Supermagnum/Tandberg/TDV-5000/tandberg.jpg

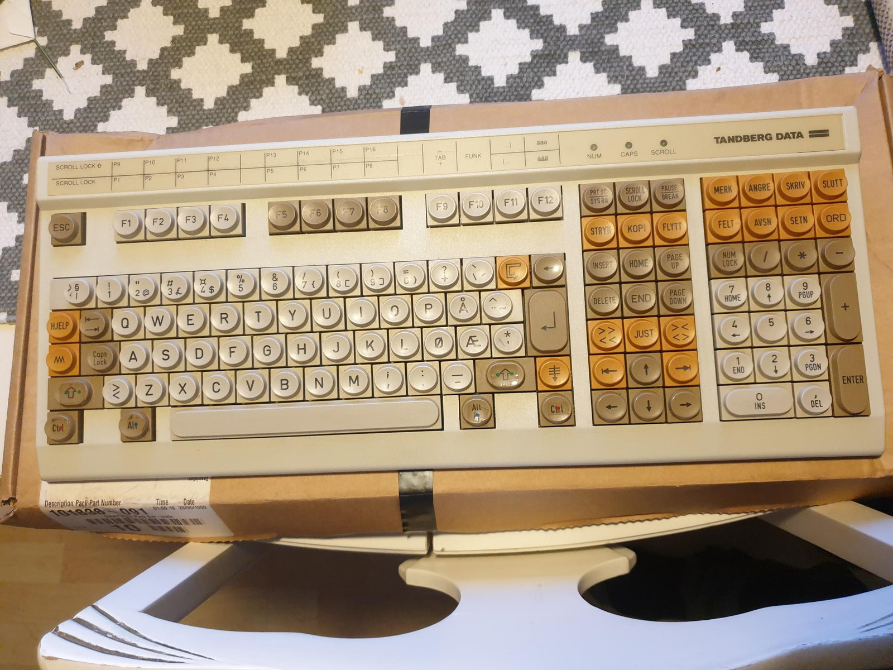
TDV-5000/tandberg.jpg
